tomcombriat/TES_e-sax/software/2b/SAX/arpegio_mono.ino

#include "arpegio_mono.h"



/*
      Combriat 2018, 2019, 2020
      This file is part of the OS embedded in the e-sax - TES
      This code is under GPL3


      This is the class file for the class managing arpegiators
*/



arpegio_mono::arpegio_mono() {}

arpegio_mono::arpegio_mono(unsigned int N, float * times, int * notes)
{
  N_note_arp = N;
  times_arp = times;
  notes_arp = notes;
  duration_scaling = int (times[N - 1] + 1);
}

arpegio_mono::arpegio_mono(unsigned int N, float * times, int * notes, char _name)
{
  N_note_arp = N;
  times_arp = times;
  notes_arp = notes;
  arp_name = _name;
  duration_scaling = int (times[N - 1] + 1);
}

void arpegio_mono::set_notes(unsigned int N, float * times, int * notes)
{
  N_note_arp = N;
  times_arp = times;
  notes_arp = notes;
  duration_scaling = int (times[N - 1] + 1);
}

void arpegio_mono::set_notes(unsigned int N, float * times, int * notes, char _name)
{
  N_note_arp = N;
  times_arp = times;
  notes_arp = notes;
  arp_name = _name;
  duration_scaling = int (times[N - 1] + 1);

}

void arpegio_mono::set_notes(unsigned int N, float * times, int * notes, char _name, String * l_name)
{
  N_note_arp = N;
  times_arp = times;
  notes_arp = notes;
  arp_name = _name;
  long_name = l_name;
  duration_scaling = int (times[N - 1] + 1);
}


void arpegio_mono::set_tempo(unsigned long temp)
{
  duration = temp;
}



bool arpegio_mono::change(byte current_note) //Now 2micros!
{

  if (current_note != 0)
  {
    if (current_note != previous_note) // restart on changing note
    {
      previous_note = current_note;
      start();
    }

    if (millis() >= next_event_time)
    {
      float next_duration = 0.;


      /*
        // Calculating the duration of the next note
        if (next_index + 1 == N_note_arp) next_duration = duration_scaling  + times_arp[0] - times_arp[next_index]; //rollback
        else next_duration = times_arp[next_index + 1] - times_arp[next_index];
      */

      // Updating the next note
      if (notes_arp[next_index] != -255)   next_note = notes_arp[next_index] + current_note;
      else next_note = 0;  //silent note


      // Calculation the time for next note
      //next_event_time += duration * next_duration ;

      if (global_mode == MODE_ARPEGIO) next_index += 1;
      else if (global_mode == MODE_ARPEGIO_RAND)
      {
        unsigned int next_index_tamp = next_index;
        while (next_index_tamp == next_index || notes_arp[next_index_tamp] == notes_arp[next_index])    next_index_tamp = random(0, N_note_arp);
        next_index = next_index_tamp;
      }


      if (next_index == N_note_arp) next_index = 0; //rollback

      if (next_index == 0) next_duration = duration_scaling  + times_arp[0] - times_arp[N_note_arp - 1]; //rollback
      else next_duration = times_arp[next_index] - times_arp[next_index - 1];


      next_silent_time = next_event_time + (( (unsigned long) (duration * next_duration * sustain_scaling)) >> 7);
      next_event_time += duration * next_duration ;


      return true;
    }
    if (millis() >= next_silent_time) next_note = 0;  // if needed to shut down the note before the end
    
  }  // if (current_note !=0)

  else {
    previous_note = 0;
    next_note = 0;
  }
  return false;  // arp not started
}



int arpegio_mono::next()
{
  return next_note;
}

int arpegio_mono::previous()
{
  return previous_note;
}

void arpegio_mono::start()
{
  start_time = millis();
  next_index = 0;
  next_event_time = start_time;
  started = true;
  paused = false;
}

void arpegio_mono::stop()
{
  next_note = 0;
  started = false;
}

char arpegio_mono::get_name()
{
  return arp_name;
}

String * arpegio_mono::get_long_name()
{
  return long_name;
}

bool arpegio_mono::is_started()
{
  return started;
}

void arpegio_mono::pause()
{
  next_note = 0;
  paused = true;
}

bool arpegio_mono::is_paused()
{
  return paused;
}

int arpegio_mono::get_duration_scaling()
{
  return duration_scaling;
}

unsigned int arpegio_mono::get_N_notes()
{
  return N_note_arp;
}

int * arpegio_mono::get_notes()
{
  return notes_arp;
}

void arpegio_mono::set_sustain_scaling(int _sustain_scaling)
{
  sustain_scaling = _sustain_scaling;
}
