tomcombriat/TES_e-sax/software/2b/SAX/analog_input.ino

#include "analog_input.h"


/*
      Combriat 2018, 2019, 2020
      This file is part of the OS embedded in the e-sax - TES
      This code is under GPL3


      This is the class file for the class managing analog_inputs
*/



analog_input::analog_input() {};


analog_input::analog_input(int _pin, int _biais, unsigned long _response_time, float _scaling_factor)
{
  pin = _pin;
  biais = _biais;
  response_time = _response_time;
  pinMode(pin, INPUT);
  scaling_factor = _scaling_factor;
  min_value = -10000;
  max_value = 10000;

}

bool analog_input::has_changed()
{
  return changed;
}

bool analog_input::update()
{
  changed = false;
  if (millis() - last_read_time > response_time)
  {
    last_read_time = millis();
    int value = analogRead(pin);
    if (inverted) value = MAX_ADC - value;

    value -= biais;
    if (value > JOYSTICK_DEAD_ZONE) value -= JOYSTICK_DEAD_ZONE;
    else if (value < JOYSTICK_DEAD_ZONE) value += JOYSTICK_DEAD_ZONE;
    else value = 0;


    value *= scaling_factor;
    if (value > max_value) value = max_value;
    else if (value < min_value) value = min_value;

    if (value != previous_raw_value)
    {
      if (previous_raw_value > 100 && value < 100) up = 1;
      else if (previous_raw_value < -100 && value > -100) up = -1;
      else up = 0;
      previous_raw_value = value;
      changed = true;
    }
  }
  return changed;
}

int analog_input::value()
{
  return previous_raw_value;
}

void analog_input::calibrate()
{
  int calib = 0;
  for (int i = 0; i < 16; i++) calib += analogRead(pin);
  calib = calib >> 4;
  if (inverted) biais = MAX_ADC - calib;
  else  biais = calib;
}

void analog_input::set_biais(int _biais)
{
  biais = _biais;
}

void analog_input::set_scaling_factor(float _scaling_factor)
{
  scaling_factor = _scaling_factor;
}

void analog_input::set_min_max(int min, int max)
{
  min_value = min;
  max_value = max;
}

int analog_input::up_down()
{
  int prev_up = up;
  up = 0;
  return prev_up;
}

void analog_input::set_invert(bool _inverted)
{
  inverted = _inverted;
}

void analog_input::compute_scaling_factor(int target)
{
  target_output = target;
  scaling_factor = 1.*target_output / input_range;
}

void analog_input::precalibrate_min_max()
{
  input_range = 0;
  biased_min = 0;
  biased_max = 0;
}

void analog_input::calibrate_min_max()
{
  int value = analogRead(pin);
  if (inverted) value = MAX_ADC - value;
  value = (value - biais) - JOYSTICK_SAFETY - JOYSTICK_DEAD_ZONE;
  if (value > biased_max) biased_max = value;
  if (value < biased_min) biased_min = value;
  /*
    input_range = min(-biased_min, biased_max);
    if (input_range < 1000) input_range=1000;*/
  set_input_range(min(-biased_min, biased_max));
}

void analog_input::set_input_range(uint16_t ir)
{
  input_range = ir;
  if (input_range < 1000) input_range = 1000;
}

uint16_t analog_input::get_input_range()
{
  return input_range;
}
