tomcombriat/TES_e-sax/software/2b/SAX/screen.h

#ifndef _screen_
#define _screen_


/*
      Combriat 2018, 2019, 2020
      This file is part of the OS embedded in the e-sax - TES
      This code is under GPL3

      
      This is the include file for the class managing the screen
*/


class screen
{
  public:
    screen();
    void draw_title_value(String title, int value);
    void draw_title_value(String title);
    void draw_title_value(String title, String value, int sub_value=0);
    void draw_title_value(String title, char value, int sub_value = 0);
    void draw_title_value(String title, char value, int N, int * values ,int sub_value = 0);
    void draw_title_value(String title, String * value, int N, int * values ,int sub_value = 0);
    void draw_single_value(String value);
    void draw_standby_screen(int8_t & _octave, int8_t & _transpose, byte _global_mode, bool _delta_mode, byte _joystick, byte _joystick_bis, unsigned int tempo);
    void draw_progress_bar(byte value);
    void draw_low_batt();

    void clear();
    void update();
    void force_update();

  private:
    unsigned long last_update_time = 0;
    int previous_keyprint = 0;
    String previous_value = "aaaa";
    String previous_title = "aaaa";
    bool changed = false;

    int octave = 0,batterie=255;
    int transpose = 0;
    byte global_mode = 0;
    bool delta_mode = 0;
    byte joystick = 0;
    byte joystick_bis = 0;
    unsigned int tempo = 0;
    int loaded_preset = 0;
};

//char global_modes[5] = {'N','E', 'A', 'C','R'};



#endif
