tomcombriat/TES_e-sax/software/2b/SAX/read_shift_reg.ino

#include "read_shift_reg.h"


/*
      Combriat 2018, 2019, 2020
      This file is part of the OS embedded in the e-sax - TES
      This code is under GPL3

      
      This is the file for the the shift registers
*/



unsigned int read_shift_regs()
{
  long bitVal;
  unsigned int bytesVal = 0;

  /* Trigger a parallel Load to latch the state of the data lines,
  */
  digitalWrite(clockEnablePin, HIGH);  // can I remove that ?
  digitalWrite(ploadPin, LOW);
  delayMicroseconds(PULSE_WIDTH_USEC);
  digitalWrite(ploadPin, HIGH);
  digitalWrite(clockEnablePin, LOW);  // and that? Yes, put to GND all the time should work

  /* Loop to read each bit value from the serial out line
     of the SN74HC165N.
  */
  for (int i = 0; i < DATA_WIDTH; i++)
  {
    bitVal = digitalRead(dataPin);
    bytesVal |= (bitVal << ((DATA_WIDTH - 1) - i));

    /* Pulse the Clock (rising edge shifts the next bit).
    */
    digitalWrite(clockPin, HIGH);
    delayMicroseconds(PULSE_WIDTH_USEC);
    digitalWrite(clockPin, LOW);
  }
  return (bytesVal);
}
