tomcombriat/TES_e-sax/software/2b/SAX/pitchbend.h

#ifndef _pitchbend_
#define _pitchbend_

#define AVERAGE 256


/*
      Combriat 2018, 2019, 2020
      This file is part of the OS embedded in the e-sax - TES
      This code is under GPL3

      
      This is the include file for the class managing pitchbend
*/


class pitchbend
{
  public:
    pitchbend();
    bool has_changed();
    void update();
    void set_value(int PB);
    int get_value();

  private:
    unsigned int last_event_time;
    int value, previous_value;
    int values[AVERAGE];
    int rolling = 0;
    bool changed;
};



#endif
